carangil/cat644/kittyos/kittyos/introm.c

unsigned char  program[]={
0x00,
0x37,
0x00,
0xf2,
0xf7,
0x01,
0x71,
0x00,
0x40,
0x00,
0xf2,
0xd4,
0x76,
0x0c,
0xff,
0x00,
0x30,
0x55,
0x0a,
0x00,
0xf7,
0x02,
0x76,
0x0c,
0x01,
0x00,
0x18,
0x66,
0xed,
0xff,
0x71,
0x7b,
0x00,
0x3b,
0x00,
0xf2,
0xf7,
0x01,
0x71,
0xf7,
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
};
