carangil/cat644/kittyos/kittyos/comm.h

/*
 * COMM.h
 *
 * Created: 7/14/2014 7:54:12 PM
 *  Author: mark
 */ 


#ifndef COMM_H_
#define COMM_H_

//Special value for high baud rate that won't fit in integer
#define COMM_11520 65535


extern chardevice_t dev_ser0;

#endif /* COMM_H_ */
