carangil/cat644/cat-os/junkcode/keycodes.h

/*
 * keycodes.h
 *
 * Created: 4/29/2014 8:45:43 PM
 *  Author: mark
 */ 


#ifndef KEYCODES_H_
#define KEYCODES_H_



#define K_SHIFT	1
#define K_UP	3
#define K_DOWN	4
#define K_LEFT	5
#define K_RIGHT 6
#define K_ESC	27

#endif /* KEYCODES_H_ */
